frodobots-org/earth-rover-mini/wiki/png/4g-module-connected.png

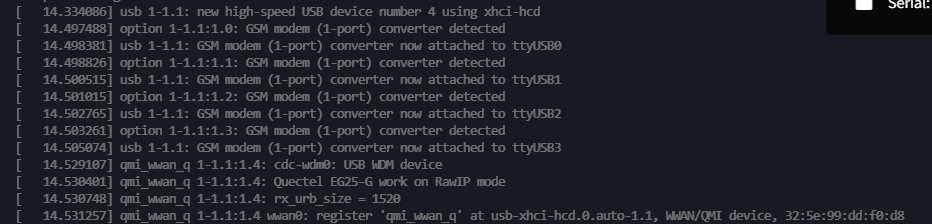
wiki/png/4g-module-connected.png
