frodobots-org/earth-rover-mini/wiki/png/4g-module-disconnected-2.png

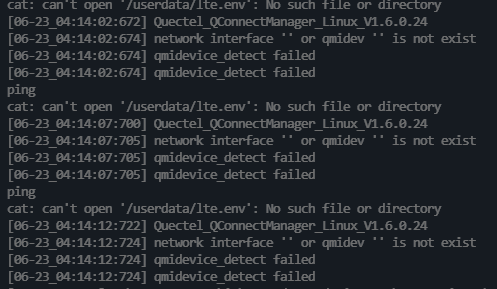
wiki/png/4g-module-disconnected-2.png
