frodobots-org/earth-rover-mini/wiki/png/4g-module-disconnected.png

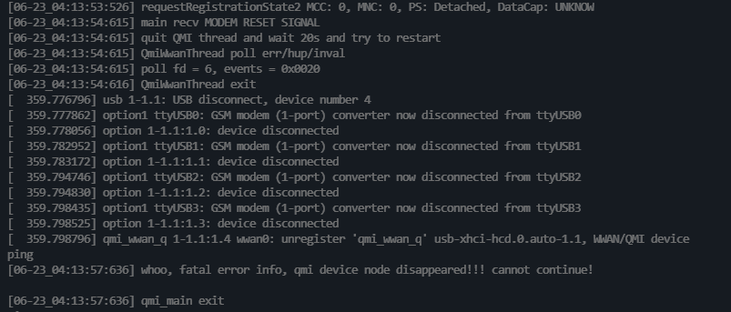
wiki/png/4g-module-disconnected.png
