frodobots-org/earth-rover-mini/wiki/png/quectel-sh.png

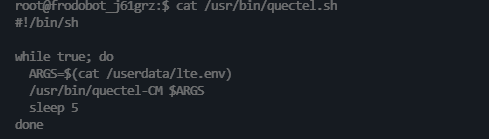
wiki/png/quectel-sh.png
