frodobots-org/earth-rover-mini/wiki/png/quectel-sim-absent.png

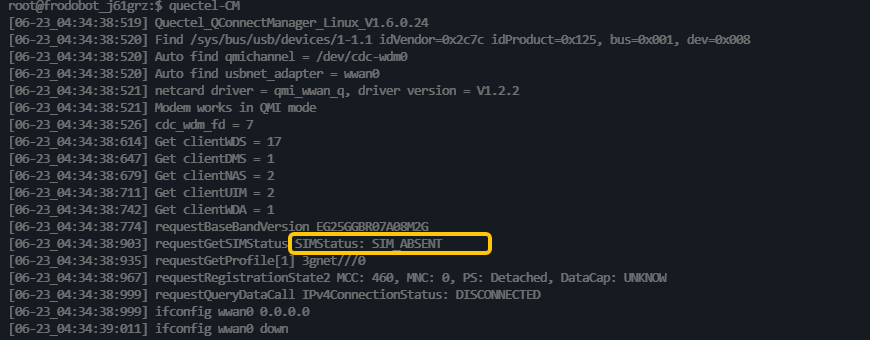
wiki/png/quectel-sim-absent.png
