frodobots-org/earth-rover-mini/Software/STM32/drivers/include/config/pwm_config.h

/*
 * Copyright (c) 2006-2018, RT-Thread Development Team
 *
 * SPDX-License-Identifier: Apache-2.0
 *
 * Change Logs:
 * Date           Author       Notes
 * 2018-12-13     zylx         first version
 */

#ifndef __PWM_CONFIG_H__
#define __PWM_CONFIG_H__

#include <rtthread.h>

#ifdef __cplusplus
extern "C" {
#endif

#ifdef BSP_USING_PWM1
#ifndef PWM1_CONFIG
#define PWM1_CONFIG                             \
    {                                           \
       .tim_handle.Instance     = TIM1,         \
       .name                    = "pwm1",       \
       .channel                 = 0             \
    }
#endif /* PWM1_CONFIG */
#endif /* BSP_USING_PWM1 */

#ifdef BSP_USING_PWM2
#ifndef PWM2_CONFIG
#define PWM2_CONFIG                             \
    {                                           \
       .tim_handle.Instance     = TIM2,         \
       .name                    = "pwm2",       \
       .channel                 = 0             \
    }
#endif /* PWM2_CONFIG */
#endif /* BSP_USING_PWM2 */

#ifdef BSP_USING_PWM3
#ifndef PWM3_CONFIG
#define PWM3_CONFIG                             \
    {                                           \
       .tim_handle.Instance     = TIM3,         \
       .name                    = "pwm3",       \
       .channel                 = 0             \
    }
#endif /* PWM3_CONFIG */
#endif /* BSP_USING_PWM3 */

#ifdef BSP_USING_PWM4
#ifndef PWM4_CONFIG
#define PWM4_CONFIG                             \
    {                                           \
       .tim_handle.Instance     = TIM4,         \
       .name                    = "pwm4",       \
       .channel                 = 0             \
    }
#endif /* PWM4_CONFIG */
#endif /* BSP_USING_PWM4 */

#ifdef BSP_USING_PWM5
#ifndef PWM5_CONFIG
#define PWM5_CONFIG                             \
    {                                           \
       .tim_handle.Instance     = TIM5,         \
       .name                    = "pwm5",       \
       .channel                 = 0             \
    }
#endif /* PWM5_CONFIG */
#endif /* BSP_USING_PWM5 */

#ifdef BSP_USING_PWM9
#ifndef PWM9_CONFIG
#define PWM9_CONFIG                             \
    {                                           \
       .tim_handle.Instance     = TIM9,         \
       .name                    = "pwm9",       \
       .channel                 = 0             \
    }
#endif /* PWM9_CONFIG */
#endif /* BSP_USING_PWM9 */

#ifdef BSP_USING_PWM10
#ifndef PWM10_CONFIG
#define PWM10_CONFIG                             \
    {                                           \
       .tim_handle.Instance     = TIM10,         \
       .name                    = "pwm10",       \
       .channel                 = 0             \
    }
#endif /* PWM10_CONFIG */
#endif /* BSP_USING_PWM10 */

#ifdef BSP_USING_PWM11
#ifndef PWM11_CONFIG
#define PWM11_CONFIG                             \
    {                                           \
       .tim_handle.Instance     = TIM11,         \
       .name                    = "pwm11",       \
       .channel                 = 0             \
    }
#endif /* PWM11_CONFIG */
#endif /* BSP_USING_PWM11 */

#ifdef BSP_USING_PWM12
#ifndef PWM12_CONFIG
#define PWM12_CONFIG                            \
    {                                           \
       .tim_handle.Instance     = TIM12,        \
       .name                    = "pwm12",      \
       .channel                 = 0             \
    }
#endif /* PWM12_CONFIG */
#endif /* BSP_USING_PWM12 */

#ifdef BSP_USING_PWM13
#ifndef PWM13_CONFIG
#define PWM13_CONFIG                            \
    {                                           \
       .tim_handle.Instance     = TIM13,        \
       .name                    = "pwm13",      \
       .channel                 = 0             \
    }
#endif /* PWM13_CONFIG */
#endif /* BSP_USING_PWM13 */
#ifdef __cplusplus
}
#endif

#endif /* __PWM_CONFIG_H__ */
