frodobots-org/earth-rover-mini/Software/STM32/applications/INA226.c

/*
 * Copyright (c) 2006-2021, RT-Thread Development Team
 *
 * SPDX-License-Identifier: Apache-2.0
 *
 * Change Logs:
 * Date           Author       Notes
 * 2024-11-21     yuxing       the first version
 */
#define DBG_TAG "INA226"
#define DBG_LVL DBG_LOG
#include "INA226.h"
#include <rtdbg.h>

#define INA226_I2CBUS_NAME  "i2c2"
struct rt_i2c_bus_device *INA226_i2c_bus;

void INA226_init(void)
{
    /********************** Software I²C Initialization ***************************/
    rt_err_t ret = 0;
    rt_uint8_t res;
    rt_device_t dev;
    dev = rt_device_find(INA226_I2CBUS_NAME);

    if (dev == RT_NULL)
    {
        LOG_E("can't find INA226 %s device\r\n", INA226_I2CBUS_NAME);
        return -RT_ERROR;
    }

    if (rt_device_open(dev, RT_DEVICE_OFLAG_RDWR) != RT_EOK)
    {
        LOG_E("can't open INA226 %s device\r\n", INA226_I2CBUS_NAME);
        return -RT_ERROR;
    }
    // Get I2C device handle
    INA226_i2c_bus = (struct rt_i2c_bus_device *)dev;
    /********************** Software I²C Initialization ***************************/

    /********************** INA226 Initialization ***************************/
    /**
    * Configure conversion time = 8.244ms, averaging = 16 samples,
    * mode = shunt + bus continuous mode
    * → Total data conversion time = 8.244 * 16 = 131.9 ms
    */
    INA226_SetConfig(0x45FF);

    /** Max current of this device ≈ 3.6A
    * Shunt voltage max = 32768 * 0.0000025V = 0.08192V
    * Set shunt voltage-to-current conversion:
    *   - Shunt resistor = 0.01Ω
    *   - Resolution = 0.2mA
    *
    * Formula 1:
    *   Current_LSB = Expected Max Current / 2^15
    *   Current_LSB = 5 / 32768 = 0.000152A (~0.15mA) → choose 0.2mA
    *
    * Formula 2:
    *   CAL = 0.00512 / (Current_LSB * R)
    *   CAL = 0.00512 / (0.0002 * 0.01) = 2560 = 0x0a00
    */
    INA226_SetCalibrationReg(0x0a00);
    /********************** INA226 Initialization ***************************/
}
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
